SolarC15-original/pasantia-/Actividades de apoyo/WhatsApp Image 2025-10-28 at 21.30.59.jpeg

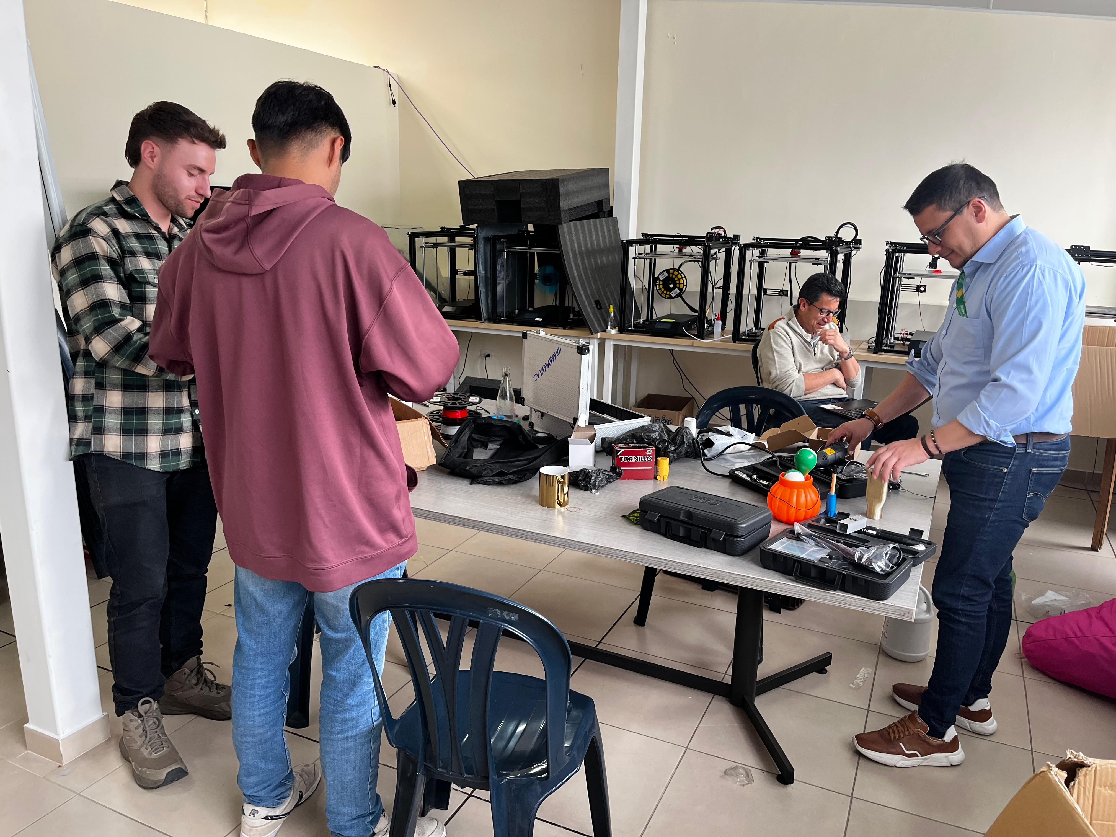
Actividades de apoyo/WhatsApp Image 2025-10-28 at 21.30.59.jpeg
